workFLOw42/3D_OralB_Sonicare_toothbrush_holder/renders/1_sonicare_laden_einzeln.png

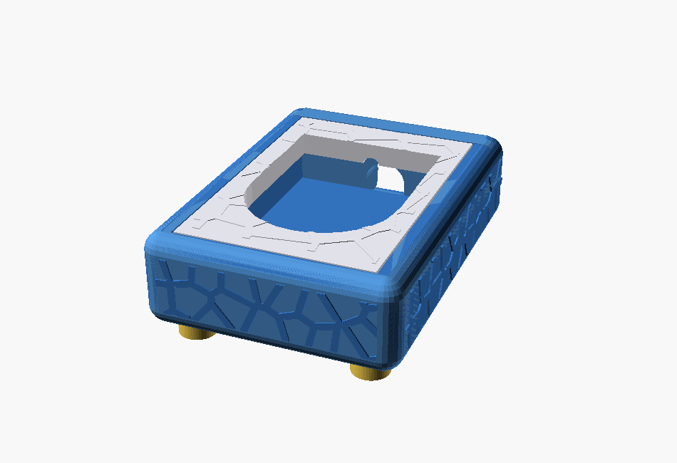
renders/1_sonicare_laden_einzeln.png
