workFLOw42/3D_OralB_Sonicare_toothbrush_holder/renders/3_sonicare_laden_staender.png

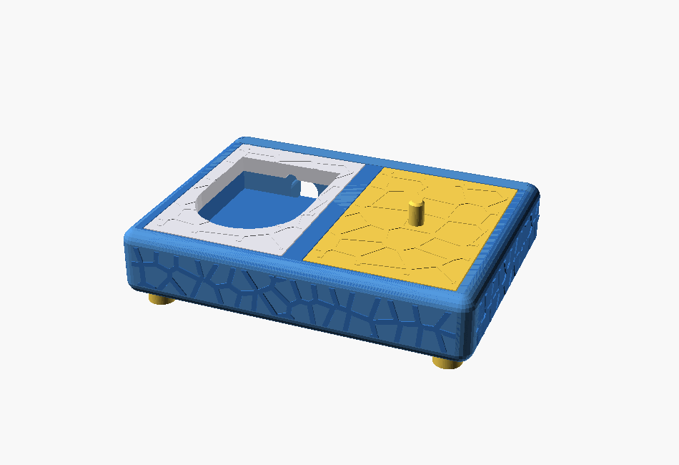
renders/3_sonicare_laden_staender.png
