workFLOw42/3D_OralB_Sonicare_toothbrush_holder/renders/PXL_20260618_064923783.RAW-01.COVER.jpg

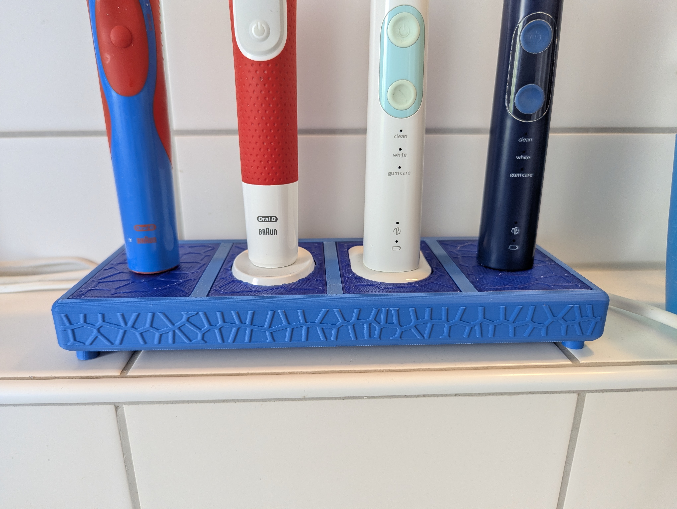
renders/PXL_20260618_064923783.RAW-01.COVER.jpg
