workFLOw42/3D_OralB_Sonicare_toothbrush_holder/voronoi_data.scad

// AUTO-GENERIERT von gen_voronoi.py - nicht von Hand editieren.
// cell_face=7.0 cell_insert=12.0 seed=7

// voro_face_long: Rechteck 237.0 x 15.0 mm, 149 Segmente
voro_face_long = [
  [8.057,0.000,4.064,1.466],
  [2.347,-0.000,4.064,1.466],
  [0.000,8.369,3.865,8.555],
  [3.865,8.555,4.064,1.466],
  [10.020,0.000,14.888,5.811],
  [14.888,5.811,19.922,0.000],
  [133.093,0.000,136.962,0.253],
  [137.360,0.000,136.962,0.253],
  [3.865,8.555,3.995,8.778],
  [2.123,15.000,3.995,8.778],
  [166.082,0.000,168.025,0.646],
  [168.590,-0.000,168.025,0.646],
  [111.004,7.512,113.559,0.000],
  [111.004,7.512,118.872,6.561],
  [118.872,6.561,117.839,0.000],
  [121.921,8.654,118.872,6.561],
  [121.921,8.654,118.935,15.000],
  [110.378,7.989,114.326,15.000],
  [110.378,7.989,111.004,7.512],
  [126.901,0.000,125.109,7.769],
  [121.921,8.654,125.109,7.769],
  [25.976,15.000,27.423,7.986],
  [27.423,7.986,29.169,7.932],
  [33.288,15.000,29.169,7.932],
  [34.285,0.000,32.543,6.090],
  [23.204,0.000,26.665,7.598],
  [27.423,7.986,26.665,7.598],
  [29.169,7.932,32.543,6.090],
  [58.137,15.000,54.575,13.526],
  [53.571,15.000,54.575,13.526],
  [90.569,0.000,90.192,0.458],
  [90.192,0.458,89.212,0.000],
  [110.378,7.989,105.568,7.750],
  [105.568,7.750,104.761,-0.000],
  [61.033,15.000,63.604,7.683],
  [54.575,13.526,53.370,10.662],
  [53.370,10.662,59.992,5.142],
  [63.604,7.683,59.992,5.142],
  [55.885,0.000,59.238,1.214],
  [54.512,0.000,48.967,7.905],
  [53.370,10.662,48.967,7.905],
  [59.992,5.142,59.238,1.214],
  [59.238,1.214,60.623,0.000],
  [17.960,15.000,17.723,10.455],
  [10.364,15.000,9.668,10.140],
  [17.723,10.455,14.856,8.271],
  [14.856,8.271,9.668,10.140],
  [26.665,7.598,17.723,10.455],
  [3.995,8.778,9.668,10.140],
  [14.888,5.811,14.856,8.271],
  [145.035,15.000,144.505,14.715],
  [147.358,4.689,152.226,6.167],
  [147.358,4.689,145.717,6.743],
  [151.956,15.000,153.767,8.089],
  [145.717,6.743,144.505,14.715],
  [153.767,8.089,152.226,6.167],
  [146.190,0.734,147.358,4.689],
  [146.190,0.734,146.662,0.000],
  [156.932,0.000,152.226,6.167],
  [143.815,0.000,146.190,0.734],
  [166.787,8.049,166.355,15.000],
  [166.787,8.049,160.843,8.137],
  [159.441,8.978,160.843,8.137],
  [159.441,8.978,159.317,15.000],
  [168.025,0.646,168.368,6.774],
  [168.368,6.774,166.787,8.049],
  [159.108,0.000,160.843,8.137],
  [153.767,8.089,159.441,8.978],
  [136.962,0.253,137.917,6.258],
  [145.717,6.743,139.674,6.896],
  [137.917,6.258,139.674,6.896],
  [144.505,14.715,143.465,15.000],
  [139.674,6.896,140.216,15.000],
  [98.829,7.247,104.569,8.550],
  [98.829,7.247,97.284,7.639],
  [97.284,7.639,94.915,15.000],
  [104.569,8.550,103.256,15.000],
  [105.568,7.750,104.569,8.550],
  [97.519,0.000,98.829,7.247],
  [90.192,0.458,88.990,5.441],
  [88.990,5.441,97.284,7.639],
  [91.075,15.000,88.353,6.113],
  [88.353,6.113,88.990,5.441],
  [68.533,15.000,69.379,9.029],
  [63.604,7.683,67.012,7.403],
  [69.379,9.029,67.012,7.403],
  [67.012,7.403,68.340,0.000],
  [181.767,7.379,183.106,0.000],
  [181.767,7.379,178.290,6.025],
  [178.290,6.025,176.867,0.000],
  [172.221,8.051,168.368,6.774],
  [172.221,8.051,178.290,6.025],
  [172.221,8.051,174.468,15.000],
  [183.264,8.683,182.609,15.000],
  [183.264,8.683,181.767,7.379],
  [132.479,8.592,126.949,9.056],
  [132.479,8.592,134.446,9.420],
  [134.446,9.420,136.463,15.000],
  [126.949,9.056,128.279,15.000],
  [132.791,0.000,132.479,8.592],
  [125.109,7.769,126.949,9.056],
  [137.917,6.258,134.446,9.420],
  [233.140,0.000,234.711,7.471],
  [234.711,7.471,237.000,8.285],
  [234.711,7.471,232.738,8.653],
  [232.738,8.653,230.881,15.000],
  [229.248,0.000,226.265,6.430],
  [232.738,8.653,227.566,7.831],
  [226.265,6.430,227.566,7.831],
  [226.265,6.430,221.327,5.935],
  [221.649,-0.000,221.327,5.935],
  [39.585,15.000,37.445,7.912],
  [43.300,15.000,48.102,7.834],
  [37.445,7.912,41.695,5.668],
  [41.695,5.668,47.411,7.165],
  [48.102,7.834,47.411,7.165],
  [32.543,6.090,37.445,7.912],
  [48.967,7.905,48.102,7.834],
  [40.139,0.000,41.695,5.668],
  [46.538,0.000,47.411,7.165],
  [79.755,0.000,81.211,7.507],
  [72.483,0.000,75.565,7.997],
  [80.625,8.016,76.900,8.469],
  [80.625,8.016,81.211,7.507],
  [76.900,8.469,75.565,7.997],
  [88.353,6.113,81.211,7.507],
  [69.379,9.029,75.565,7.997],
  [82.241,15.000,80.625,8.016],
  [74.912,15.000,76.900,8.469],
  [227.566,7.831,225.062,15.000],
  [221.327,5.935,218.227,8.687],
  [218.227,8.687,222.535,15.000],
  [215.134,8.479,212.271,4.887],
  [215.134,8.479,211.153,15.000],
  [204.736,7.393,205.663,15.000],
  [204.736,7.393,206.931,5.724],
  [206.931,5.724,212.271,4.887],
  [218.227,8.687,215.134,8.479],
  [198.014,0.000,197.398,5.551],
  [188.447,0.000,188.537,6.631],
  [188.537,6.631,192.841,7.801],
  [192.841,7.801,196.324,6.721],
  [197.398,5.551,196.324,6.721],
  [204.736,7.393,197.398,5.551],
  [204.362,0.000,206.931,5.724],
  [183.264,8.683,188.537,6.631],
  [192.095,15.000,192.841,7.801],
  [199.903,15.000,196.324,6.721],
  [212.271,4.887,212.717,0.000]
];

// voro_face_short: Rechteck 84.0 x 15.0 mm, 49 Segmente
voro_face_short = [
  [84.000,7.584,79.073,8.229],
  [79.073,8.229,80.166,0.000],
  [41.132,10.006,41.830,15.000],
  [41.132,10.006,37.168,8.598],
  [37.168,8.598,33.151,15.000],
  [18.123,7.039,28.105,6.773],
  [18.123,7.039,19.908,14.856],
  [28.105,6.773,26.802,15.000],
  [19.908,14.856,20.191,15.000],
  [17.433,6.337,18.123,7.039],
  [17.433,6.337,11.642,7.244],
  [19.485,15.000,19.908,14.856],
  [9.844,15.000,11.642,7.244],
  [34.946,5.937,29.161,5.498],
  [34.946,5.937,37.711,0.000],
  [29.161,5.498,27.069,0.000],
  [37.168,8.598,34.946,5.937],
  [28.105,6.773,29.161,5.498],
  [17.433,6.337,18.742,0.000],
  [65.309,5.782,65.117,0.000],
  [65.309,5.782,71.157,6.176],
  [71.157,6.176,72.231,0.000],
  [63.160,7.056,65.309,5.782],
  [63.160,7.056,57.741,5.035],
  [57.741,5.035,57.181,0.000],
  [56.046,6.386,48.262,7.231],
  [56.046,6.386,56.332,15.000],
  [48.262,7.231,50.955,15.000],
  [57.741,5.035,56.046,6.386],
  [51.398,-0.000,47.766,6.936],
  [47.766,6.936,48.262,7.231],
  [41.132,10.006,46.619,6.740],
  [46.619,6.740,47.766,6.936],
  [81.071,15.000,78.540,8.800],
  [78.540,8.800,73.718,8.863],
  [73.718,8.863,70.419,15.000],
  [79.073,8.229,78.540,8.800],
  [71.157,6.176,73.718,8.863],
  [63.228,14.438,64.518,15.000],
  [63.228,14.438,61.974,15.000],
  [63.160,7.056,63.228,14.438],
  [3.812,15.000,3.265,6.064],
  [11.642,7.244,9.586,5.534],
  [9.586,5.534,3.265,6.064],
  [9.586,5.534,9.741,0.000],
  [46.619,6.740,43.679,0.000],
  [3.755,0.000,3.036,5.911],
  [0.000,5.637,3.036,5.911],
  [3.265,6.064,3.036,5.911]
];

// voro_insert: Rechteck 57.0 x 79.0 mm, 84 Segmente
voro_insert = [
  [0.000,72.754,5.210,72.672],
  [5.210,72.672,6.730,71.460],
  [6.730,71.460,8.123,60.556],
  [0.000,61.509,8.123,60.556],
  [8.308,79.000,5.210,72.672],
  [17.599,79.000,19.310,71.867],
  [19.310,71.867,6.730,71.460],
  [0.000,45.682,6.312,43.758],
  [10.060,59.330,8.123,60.556],
  [10.060,59.330,7.883,45.322],
  [6.312,43.758,7.883,45.322],
  [57.000,42.860,51.714,42.379],
  [57.000,31.505,49.360,30.993],
  [51.714,42.379,49.360,30.993],
  [10.060,59.330,20.947,63.304],
  [19.310,71.867,21.929,68.230],
  [21.929,68.230,20.947,63.304],
  [21.929,68.230,33.984,73.375],
  [34.191,79.000,33.984,73.375],
  [33.737,0.000,36.830,1.490],
  [36.830,1.490,38.199,0.000],
  [7.883,45.322,23.361,47.310],
  [20.947,63.304,23.478,59.402],
  [23.478,59.402,23.849,47.834],
  [23.849,47.834,23.361,47.310],
  [33.984,73.375,35.780,72.118],
  [35.780,72.118,47.904,74.200],
  [47.904,74.200,48.408,79.000],
  [49.717,55.894,46.873,60.235],
  [49.717,55.894,48.239,45.800],
  [48.239,45.800,37.570,44.950],
  [46.873,60.235,40.328,61.129],
  [37.570,44.950,36.298,46.216],
  [36.298,46.216,37.004,58.090],
  [40.328,61.129,37.004,58.090],
  [57.000,56.347,49.717,55.894],
  [52.323,69.154,57.000,69.614],
  [52.323,69.154,46.873,60.235],
  [51.714,42.379,48.239,45.800],
  [48.082,29.012,37.056,31.730],
  [48.082,29.012,49.360,30.993],
  [37.056,31.730,35.474,33.869],
  [35.474,33.869,37.570,44.950],
  [35.780,72.118,40.328,61.129],
  [52.323,69.154,47.904,74.200],
  [35.474,33.869,23.921,34.048],
  [23.921,34.048,23.361,47.310],
  [23.849,47.834,36.298,46.216],
  [23.478,59.402,37.004,58.090],
  [57.000,9.612,52.914,4.929],
  [57.000,18.998,50.079,21.452],
  [52.914,4.929,44.356,13.049],
  [44.356,13.049,47.307,18.708],
  [47.307,18.708,50.079,21.452],
  [52.636,0.000,52.914,4.929],
  [48.082,29.012,50.079,21.452],
  [36.228,7.737,44.356,13.049],
  [36.228,7.737,36.830,1.490],
  [37.056,31.730,33.336,22.303],
  [33.336,22.303,47.307,18.708],
  [19.659,5.706,17.790,9.379],
  [19.659,5.706,35.991,7.933],
  [17.790,9.379,24.205,19.245],
  [35.991,7.933,29.077,18.203],
  [29.077,18.203,24.205,19.245],
  [19.831,0.000,19.659,5.706],
  [36.228,7.737,35.991,7.933],
  [33.336,22.303,29.077,18.203],
  [6.312,43.758,6.965,39.808],
  [0.000,31.316,6.965,39.808],
  [0.000,8.806,6.260,8.531],
  [6.260,8.531,6.478,0.000],
  [8.143,10.615,17.790,9.379],
  [8.143,10.615,6.260,8.531],
  [7.152,18.640,22.253,21.849],
  [7.152,18.640,5.559,20.979],
  [5.559,20.979,13.684,32.257],
  [13.684,32.257,20.169,30.490],
  [20.169,30.490,22.253,21.849],
  [8.143,10.615,7.152,18.640],
  [24.205,19.245,22.253,21.849],
  [0.000,23.061,5.559,20.979],
  [6.965,39.808,13.684,32.257],
  [23.921,34.048,20.169,30.490]
];

// voro_cup_w: Rechteck 46.2 x 70.0 mm, 177 Segmente
voro_cup_w = [
  [5.162,49.504,7.325,42.529],
  [5.162,49.504,4.019,49.934],
  [7.325,42.529,4.565,40.190],
  [0.000,41.411,4.565,40.190],
  [4.019,49.934,0.000,47.957],
  [0.000,5.784,2.776,5.409],
  [3.219,0.000,2.776,5.409],
  [23.326,34.614,27.277,26.845],
  [23.326,34.614,24.214,35.353],
  [24.214,35.353,35.027,36.595],
  [35.027,36.595,31.506,27.342],
  [27.277,26.845,31.506,27.342],
  [34.428,3.896,41.847,1.001],
  [34.428,3.896,34.170,3.736],
  [32.794,0.000,34.170,3.736],
  [41.847,1.001,42.017,0.000],
  [46.200,48.686,43.556,48.369],
  [41.428,44.933,43.556,48.369],
  [41.428,44.933,43.749,40.601],
  [43.749,40.601,46.200,41.462],
  [41.742,62.334,42.712,58.570],
  [41.742,62.334,46.200,64.499],
  [42.712,58.570,46.200,57.480],
  [41.742,62.334,39.522,65.292],
  [39.522,65.292,41.997,70.000],
  [4.565,40.190,5.118,35.541],
  [-0.000,33.629,2.449,32.409],
  [5.118,35.541,2.449,32.409],
  [11.919,42.724,7.325,42.529],
  [11.919,42.724,11.639,32.505],
  [5.118,35.541,11.639,32.505],
  [0.000,28.357,2.057,29.351],
  [2.057,29.351,2.449,32.409],
  [23.326,34.614,23.076,34.672],
  [27.277,26.845,26.954,26.360],
  [16.151,27.008,23.076,34.672],
  [16.151,27.008,18.511,25.118],
  [18.511,25.118,26.954,26.360],
  [41.847,1.001,43.850,4.604],
  [43.850,4.604,46.200,5.582],
  [34.170,3.736,26.846,5.400],
  [26.846,5.400,25.649,4.098],
  [25.863,0.000,25.649,4.098],
  [34.428,3.896,35.682,10.700],
  [26.846,5.400,27.163,12.553],
  [27.163,12.553,35.682,10.700],
  [39.749,10.530,36.118,10.986],
  [39.749,10.530,43.850,4.604],
  [35.682,10.700,36.118,10.986],
  [4.019,49.934,1.074,56.832],
  [1.074,56.832,0.000,57.094],
  [38.993,35.919,42.914,38.161],
  [38.993,35.919,41.257,28.137],
  [42.914,38.161,46.200,35.372],
  [41.257,28.137,46.200,28.260],
  [35.135,36.696,35.027,36.595],
  [35.135,36.696,38.993,35.919],
  [40.381,27.275,34.528,25.736],
  [40.381,27.275,41.257,28.137],
  [31.506,27.342,34.528,25.736],
  [43.749,40.601,42.914,38.161],
  [40.381,27.275,42.280,19.176],
  [46.200,20.180,42.280,19.176],
  [34.528,25.736,35.598,19.104],
  [36.579,18.222,35.598,19.104],
  [36.579,18.222,42.197,19.083],
  [42.197,19.083,42.280,19.176],
  [39.749,10.530,43.349,13.386],
  [36.118,10.986,36.579,18.222],
  [42.197,19.083,43.349,13.386],
  [34.705,53.628,34.619,51.674],
  [34.705,53.628,42.675,58.525],
  [34.619,51.674,42.700,49.854],
  [42.675,58.525,42.700,49.854],
  [42.712,58.570,42.675,58.525],
  [43.556,48.369,42.700,49.854],
  [35.506,45.705,33.871,49.343],
  [35.506,45.705,33.772,41.084],
  [33.871,49.343,29.706,48.590],
  [29.706,48.590,25.991,44.762],
  [33.772,41.084,27.307,41.977],
  [25.991,44.762,27.307,41.977],
  [41.428,44.933,35.506,45.705],
  [34.619,51.674,33.871,49.343],
  [35.135,36.696,33.772,41.084],
  [24.214,35.353,27.307,41.977],
  [39.522,65.292,36.506,65.687],
  [36.506,65.687,33.723,67.996],
  [33.723,67.996,32.719,70.000],
  [26.145,56.433,20.347,60.911],
  [26.145,56.433,30.321,57.934],
  [30.340,58.042,27.290,64.196],
  [30.340,58.042,30.321,57.934],
  [24.962,65.235,27.290,64.196],
  [24.962,65.235,20.205,63.295],
  [20.205,63.295,20.347,60.911],
  [24.707,53.084,26.145,56.433],
  [24.707,53.084,29.706,48.590],
  [34.705,53.628,30.321,57.934],
  [36.506,65.687,30.340,58.042],
  [33.723,67.996,27.290,64.196],
  [26.001,70.000,24.962,65.235],
  [17.688,65.713,18.551,70.000],
  [17.688,65.713,20.205,63.295],
  [12.816,43.108,12.173,49.078],
  [12.816,43.108,17.215,42.536],
  [12.173,49.078,19.169,51.319],
  [17.215,42.536,20.634,46.476],
  [20.634,46.476,20.427,50.245],
  [20.427,50.245,19.169,51.319],
  [5.162,49.504,9.913,52.240],
  [11.919,42.724,12.816,43.108],
  [9.913,52.240,12.173,49.078],
  [19.694,36.738,11.859,32.265],
  [19.694,36.738,17.215,42.536],
  [11.639,32.505,11.859,32.265],
  [11.123,56.250,16.432,55.850],
  [11.123,56.250,9.913,52.240],
  [16.432,55.850,19.169,51.319],
  [19.694,36.738,23.076,34.672],
  [25.991,44.762,20.634,46.476],
  [24.707,53.084,20.427,50.245],
  [16.432,55.850,20.347,60.911],
  [2.776,5.409,5.000,8.111],
  [5.000,8.111,4.753,11.612],
  [4.753,11.612,3.709,12.992],
  [0.000,13.180,3.709,12.992],
  [11.717,21.192,12.400,27.681],
  [11.717,21.192,10.283,19.567],
  [10.283,19.567,4.959,19.355],
  [5.335,26.631,12.094,28.026],
  [5.335,26.631,4.181,20.363],
  [4.181,20.363,4.959,19.355],
  [12.400,27.681,12.094,28.026],
  [4.753,11.612,12.671,13.588],
  [12.671,13.588,10.283,19.567],
  [3.709,12.992,4.959,19.355],
  [2.057,29.351,5.335,26.631],
  [11.859,32.265,12.094,28.026],
  [0.000,21.059,4.181,20.363],
  [16.151,27.008,12.400,27.681],
  [18.511,25.118,18.392,20.370],
  [11.717,21.192,17.559,19.507],
  [17.559,19.507,18.392,20.370],
  [26.954,26.360,26.060,19.428],
  [18.392,20.370,26.060,19.428],
  [27.163,12.553,26.216,13.794],
  [35.598,19.104,26.812,17.064],
  [26.216,13.794,26.812,17.064],
  [26.060,19.428,26.812,17.064],
  [17.688,65.713,11.761,65.224],
  [11.123,56.250,10.635,56.925],
  [11.761,65.224,10.635,56.925],
  [1.074,56.832,4.563,58.217],
  [10.635,56.925,4.563,58.217],
  [43.349,13.386,46.200,12.672],
  [10.494,5.616,11.738,2.458],
  [10.494,5.616,15.346,12.156],
  [11.738,2.458,18.020,3.400],
  [15.346,12.156,17.254,12.219],
  [19.178,5.043,18.020,3.400],
  [19.178,5.043,17.816,11.922],
  [17.254,12.219,17.816,11.922],
  [5.000,8.111,10.494,5.616],
  [10.715,0.000,11.738,2.458],
  [12.671,13.588,15.346,12.156],
  [18.890,0.000,18.020,3.400],
  [17.559,19.507,17.254,12.219],
  [25.649,4.098,19.178,5.043],
  [26.216,13.794,17.816,11.922],
  [10.604,70.000,10.608,66.124],
  [10.608,66.124,5.400,65.885],
  [2.980,70.000,3.218,67.089],
  [5.400,65.885,3.218,67.089],
  [11.761,65.224,10.608,66.124],
  [4.563,58.217,5.400,65.885],
  [0.000,65.556,3.218,67.089]
];

// voro_cup_d: Rechteck 67.9 x 70.0 mm, 263 Segmente
voro_cup_d = [
  [48.671,49.073,49.708,45.558],
  [48.671,49.073,55.658,51.764],
  [49.708,45.558,55.942,42.647],
  [55.658,51.764,58.201,48.764],
  [58.201,48.764,57.641,43.630],
  [55.942,42.647,57.641,43.630],
  [67.900,18.614,63.843,17.512],
  [63.843,17.512,64.398,25.670],
  [64.398,25.670,67.900,26.379],
  [49.708,45.558,47.758,42.204],
  [55.942,42.647,54.657,35.038],
  [47.758,42.204,47.982,37.798],
  [47.982,37.798,53.639,34.839],
  [53.639,34.839,54.657,35.038],
  [0.000,20.843,1.818,21.049],
  [1.818,21.049,2.668,27.201],
  [0.000,27.988,2.668,27.201],
  [47.698,56.544,41.218,59.987],
  [47.698,56.544,47.343,50.111],
  [41.218,59.987,39.369,51.817],
  [47.343,50.111,42.018,49.391],
  [42.018,49.391,39.369,51.817],
  [64.914,42.865,67.900,42.612],
  [64.914,42.865,64.047,42.089],
  [64.047,42.089,63.929,36.709],
  [67.900,34.596,64.937,35.703],
  [63.929,36.709,64.937,35.703],
  [65.553,50.686,65.581,50.729],
  [65.553,50.686,64.914,42.865],
  [67.900,51.083,65.581,50.729],
  [58.201,48.764,65.553,50.686],
  [57.641,43.630,64.047,42.089],
  [56.097,34.225,54.657,35.038],
  [56.097,34.225,63.929,36.709],
  [64.398,25.670,62.039,26.853],
  [62.039,26.853,64.937,35.703],
  [62.039,26.853,59.152,27.113],
  [59.152,27.113,56.097,34.225],
  [48.331,70.000,49.462,66.029],
  [54.161,70.000,54.366,67.058],
  [54.366,67.058,49.462,66.029],
  [67.900,66.142,63.866,67.510],
  [63.866,67.510,63.560,70.000],
  [63.259,55.011,65.266,58.020],
  [63.259,55.011,57.173,57.203],
  [65.266,58.020,61.276,65.328],
  [57.173,57.203,56.458,58.676],
  [56.458,58.676,58.299,63.976],
  [61.276,65.328,58.299,63.976],
  [65.581,50.729,63.259,55.011],
  [67.900,59.096,65.266,58.020],
  [55.658,51.764,57.173,57.203],
  [63.866,67.510,61.276,65.328],
  [48.671,49.073,47.343,50.111],
  [47.698,56.544,50.432,58.645],
  [50.432,58.645,56.458,58.676],
  [50.432,58.645,48.449,65.019],
  [54.366,67.058,58.299,63.976],
  [48.449,65.019,49.462,66.029],
  [41.218,59.987,40.957,60.445],
  [39.369,51.817,35.087,52.075],
  [40.957,60.445,34.765,59.669],
  [34.765,59.669,33.244,57.356],
  [33.244,57.356,35.087,52.075],
  [2.668,27.201,3.856,27.901],
  [3.856,27.901,3.819,34.218],
  [3.819,34.218,0.000,35.006],
  [48.449,65.019,43.150,64.937],
  [43.150,64.937,43.332,70.000],
  [40.957,60.445,41.715,63.682],
  [43.150,64.937,41.715,63.682],
  [59.152,27.113,55.311,23.287],
  [53.639,34.839,49.639,29.764],
  [49.639,29.764,55.311,23.287],
  [47.982,37.798,41.241,34.367],
  [41.241,34.367,42.005,29.493],
  [42.005,29.493,45.026,28.357],
  [49.639,29.764,45.026,28.357],
  [63.843,17.512,63.758,17.387],
  [67.900,10.785,64.480,10.505],
  [64.480,10.505,63.001,12.772],
  [63.758,17.387,63.001,12.772],
  [55.311,23.287,54.996,22.442],
  [63.758,17.387,54.996,22.442],
  [67.900,3.656,64.135,3.599],
  [64.135,3.599,64.570,0.000],
  [64.480,10.505,63.174,5.560],
  [63.174,5.560,64.135,3.599],
  [42.981,1.537,42.995,-0.000],
  [42.981,1.537,48.818,3.531],
  [48.693,0.000,48.818,3.531],
  [4.744,70.000,2.577,65.260],
  [2.577,65.260,0.000,64.523],
  [32.768,49.796,27.618,51.202],
  [32.768,49.796,33.208,44.038],
  [27.618,51.202,26.298,42.529],
  [33.208,44.038,26.298,42.529],
  [33.425,43.886,33.595,35.752],
  [33.425,43.886,39.452,43.480],
  [40.061,42.475,40.641,34.992],
  [40.061,42.475,39.452,43.480],
  [40.641,34.992,33.595,35.752],
  [42.018,49.391,39.452,43.480],
  [35.087,52.075,32.768,49.796],
  [33.208,44.038,33.425,43.886],
  [47.758,42.204,40.061,42.475],
  [41.241,34.367,40.641,34.992],
  [42.005,29.493,40.043,27.632],
  [30.617,34.035,33.595,35.752],
  [30.617,34.035,37.463,26.310],
  [37.463,26.310,40.043,27.632],
  [25.959,42.299,27.880,33.581],
  [25.959,42.299,21.326,43.320],
  [18.258,41.453,21.326,43.320],
  [18.258,41.453,17.843,34.750],
  [17.843,34.750,27.652,33.322],
  [27.652,33.322,27.880,33.581],
  [30.617,34.035,27.880,33.581],
  [26.298,42.529,25.959,42.299],
  [26.753,27.125,34.973,23.670],
  [26.753,27.125,27.652,33.322],
  [37.463,26.310,34.973,23.670],
  [34.726,70.000,34.490,69.070],
  [34.490,69.070,31.171,66.145],
  [27.122,70.000,26.980,65.768],
  [26.980,65.768,31.171,66.145],
  [41.715,63.682,34.490,69.070],
  [34.765,59.669,31.171,66.145],
  [18.919,70.000,19.142,68.958],
  [19.142,68.958,26.814,65.685],
  [26.814,65.685,26.980,65.768],
  [42.981,1.537,38.773,5.202],
  [41.341,10.719,49.306,8.971],
  [41.341,10.719,40.801,10.246],
  [48.818,3.531,49.517,4.017],
  [40.801,10.246,38.773,5.202],
  [49.306,8.971,49.517,4.017],
  [54.500,0.000,54.245,1.559],
  [49.517,4.017,54.245,1.559],
  [63.174,5.560,57.692,4.518],
  [57.692,4.518,54.245,1.559],
  [55.225,13.656,53.220,20.507],
  [55.225,13.656,53.356,11.540],
  [53.356,11.540,50.562,10.346],
  [50.562,10.346,46.090,18.337],
  [53.220,20.507,48.549,20.490],
  [48.549,20.490,46.090,18.337],
  [63.001,12.772,55.225,13.656],
  [54.996,22.442,53.220,20.507],
  [57.692,4.518,53.356,11.540],
  [49.306,8.971,50.562,10.346],
  [41.341,10.719,42.323,16.592],
  [42.323,16.592,43.749,17.638],
  [43.749,17.638,46.090,18.337],
  [45.026,28.357,48.549,20.490],
  [40.043,27.632,43.749,17.638],
  [26.753,27.125,26.113,26.574],
  [17.258,34.101,18.249,29.263],
  [17.258,34.101,17.843,34.750],
  [26.113,26.574,22.018,25.519],
  [18.249,29.263,22.018,25.519],
  [26.113,26.574,27.485,16.580],
  [22.018,25.519,20.250,22.839],
  [20.250,22.839,26.585,15.295],
  [27.485,16.580,26.585,15.295],
  [34.973,23.670,34.940,20.236],
  [27.485,16.580,34.940,20.236],
  [42.323,16.592,35.166,19.967],
  [40.801,10.246,34.947,13.117],
  [34.947,13.117,35.166,19.967],
  [35.166,19.967,34.940,20.236],
  [0.000,5.762,1.394,5.513],
  [1.394,5.513,4.019,0.447],
  [4.019,0.447,3.574,-0.000],
  [9.492,70.000,12.026,65.419],
  [2.577,65.260,6.062,62.767],
  [6.062,62.767,12.026,65.419],
  [19.142,68.958,16.493,65.371],
  [16.493,65.371,12.840,65.175],
  [12.026,65.419,12.840,65.175],
  [6.062,62.767,7.012,60.168],
  [7.012,60.168,10.519,58.463],
  [12.840,65.175,11.197,58.759],
  [10.519,58.463,11.197,58.759],
  [16.493,65.371,17.891,58.671],
  [11.197,58.759,17.891,58.671],
  [11.897,22.397,13.141,20.961],
  [11.897,22.397,3.425,19.292],
  [13.141,20.961,8.282,11.441],
  [3.425,19.292,3.880,13.753],
  [3.880,13.753,5.942,11.912],
  [8.282,11.441,5.942,11.912],
  [18.249,29.263,11.452,24.341],
  [20.250,22.839,15.940,20.141],
  [15.940,20.141,13.141,20.961],
  [11.452,24.341,11.897,22.397],
  [1.818,21.049,3.425,19.292],
  [3.856,27.901,9.463,27.252],
  [9.463,27.252,11.452,24.341],
  [0.000,13.291,3.880,13.753],
  [1.394,5.513,5.942,11.912],
  [15.940,20.141,18.995,13.826],
  [8.282,11.441,10.836,9.124],
  [18.995,13.826,10.836,9.124],
  [34.947,13.117,30.143,10.822],
  [26.585,15.295,25.913,13.175],
  [30.143,10.822,25.913,13.175],
  [18.995,13.826,21.165,12.909],
  [21.165,12.909,25.624,13.020],
  [25.913,13.175,25.624,13.020],
  [17.258,34.101,12.319,33.449],
  [18.258,41.453,11.162,44.299],
  [11.162,44.299,10.206,43.591],
  [10.206,43.591,12.319,33.449],
  [3.819,34.218,5.688,35.910],
  [9.463,27.252,11.653,33.049],
  [5.688,35.910,11.653,33.049],
  [11.653,33.049,12.319,33.449],
  [7.012,60.168,4.703,56.435],
  [4.703,56.435,0.000,58.527],
  [10.519,58.463,10.477,51.338],
  [10.477,51.338,4.968,52.638],
  [4.703,56.435,4.968,52.638],
  [20.953,47.874,16.851,52.474],
  [20.953,47.874,26.626,52.180],
  [16.851,52.474,19.161,57.162],
  [19.161,57.162,24.748,57.623],
  [26.626,52.180,25.547,56.855],
  [24.748,57.623,25.547,56.855],
  [21.326,43.320,20.953,47.874],
  [11.162,44.299,11.658,50.285],
  [11.658,50.285,16.851,52.474],
  [27.618,51.202,26.626,52.180],
  [10.477,51.338,11.658,50.285],
  [17.891,58.671,19.161,57.162],
  [26.814,65.685,24.748,57.623],
  [33.244,57.356,25.547,56.855],
  [4.019,0.447,5.167,0.506],
  [5.167,0.506,11.643,4.653],
  [10.836,9.124,11.900,5.052],
  [11.643,4.653,11.900,5.052],
  [38.773,5.202,34.071,3.676],
  [30.143,10.822,33.857,3.773],
  [34.071,3.676,33.857,3.773],
  [0.123,49.878,0.000,49.887],
  [0.123,49.878,6.354,42.314],
  [0.000,40.419,5.762,41.501],
  [5.762,41.501,6.354,42.314],
  [4.968,52.638,0.123,49.878],
  [10.206,43.591,6.354,42.314],
  [5.688,35.910,5.762,41.501],
  [21.165,12.909,18.715,5.731],
  [11.900,5.052,15.805,4.169],
  [18.715,5.731,15.805,4.169],
  [25.624,13.020,24.458,4.081],
  [18.715,5.731,24.458,4.081],
  [33.857,3.773,25.580,1.742],
  [24.458,4.081,25.580,1.742],
  [5.167,0.506,5.563,0.000],
  [11.643,4.653,12.386,0.000],
  [34.071,3.676,34.198,0.000],
  [15.805,4.169,18.533,0.000],
  [25.580,1.742,24.803,0.000]
];

voro_dims = [[247.00,25.00],[94.00,25.00],[57.00,79.00]];
